Alberto-00/PassChain-IoT/UnlockerBoard/unlocker_sketch/unlocker_loop.ino

void loop(){
  /*************************
  * blockScreen_module loop *
  *************************/
  if(isInactive_device()){
    blockScreen();
  }


 /*************************
  * bluetooth_module loop *
  *************************/
  if(!bleKeyboard.isConnected()){
    if(!connection_status){
      check_connection();
      connection_status = true;
    }
  } else{
    if(connection_status)
      check_connection();
      
    tft.setCursor(0, 30);
    tft.print("Select the place where to write\r\nand press the\r\nbottom button.");
    
    if(buttonState2 == LOW){
      write_button();
    }
    connection_status = false;
  }
}
