Alberto-00/PassChain-IoT/PassChain_Esp32/PassChain_sketches/e_bluetooth_module.ino

bool check_connection() {
  unsigned long count = 0;
 
  while(true){
    tft.setCursor(5, 47);
    tft.fillRect(0,25,235,110,TFT_BLACK);
    
    tft.print("Connecting.");
    delay(400);
    tft.print(".");
    delay(400);
    tft.print(".");
    delay(400);
    tft.print(".");
    delay(400);
    
    if(bleKeyboard.isConnected()) {
      tft.setCursor(5, 47);
      tft.fillRect(0,25,235,110,TFT_BLACK);
      tft.print("The device is");
      tft.setCursor(5, 74);
      tft.print("connected !");
      tft_logo.pushImage(90, 84, 42, 48, bluetooth);

      delay(2700);
      
      tft.fillRect(0,25,235,110,TFT_BLACK);
      return true;
    }
    
    count++;
    if(count == 3){
      tft.setCursor(5, 47);
      tft.fillRect(0,25,235,110,TFT_BLACK);
      tft.print("Connection");
      tft.setCursor(5, 74);
      tft.print("Failed !");

      tft.setCursor(5, 122);
      tft.print("Bluetooth off.");
      delay(2800);
      return false;
    }
  }
}

void write_button(String type, String credentials){
  tft.setCursor(5, 60);
  tft.fillRect(0,25,235,110,TFT_BLACK);
  
  tft.print("Writing");
  tft.setCursor(5, 88); 
  tft.print(type);
  tft.print("."); delay(370);
  
  bleKeyboard.print(credentials);
    
  tft.print("."); delay(370);
  tft.print("."); delay(370);
  tft.print(".");
  tft.fillRect(0,25,235,110,TFT_BLACK);
}


/*void sendSequence(String sequence){
  int len = sequence.length();
  int special=0;
  for (int i=0;i<=len;i++) {
    if (special == 1) {
      if (sequence.charAt(i) == 'r') {special=0;bleKeyboard.write(KEY_RETURN);Serial.println("[KEY_RETURN]");}    //add CR
      else if (sequence.charAt(i) == 's') {special=0;bleKeyboard.write(32);Serial.println("[SPACE]");}    //add space
      else if (sequence.charAt(i) == 'c') {special=0;bleKeyboard.write(':');Serial.println(":");}    //add colon
      else if (sequence.charAt(i) == 't') {special=0;bleKeyboard.write(KEY_TAB);Serial.println("[KEY_TAB]");}       //add horizontal tab
      else if (sequence.charAt(i) == '\\') {special=1;bleKeyboard.print('\\');Serial.println("[\\]");}       //Dual slash situation
      else {
        special=0;
        bleKeyboard.print("\\");
        bleKeyboard.print(sequence.charAt(i));
      }        
    }        
    else {
      if(sequence.charAt(i) == '\\')
        special=1;
      
      else 
        bleKeyboard.print(sequence.charAt(i));
      
      bleKeyboard.releaseAll();
      delay(20);
    }
  }
}*/
